sakuyuki1341/wings_steer/各種プログラムテスト/シリアル通信テスト/serial_test_09/read_me.txt

成功したビルド

コマンドラインを実装するための関数群を別ファイルに移行するテスト
