sakuyuki1341/wings_steer/master/steering_master_ver.1.0/analog_stick_ver.1.0.ino

///
/// アナログスティックに関するファイル
///
/****************************************************
 * マクロ部
 ****************************************************/
#include "subs_ver.1.0.h"

/****************************************************
 * 構造体宣言部
 ****************************************************/

/****************************************************
 * 独自関数部
 ****************************************************/
//アナログスティック関連の初期設定
void init_stick() {
	pinMode(PIN_AS_SW, INPUT_PULLUP);
}

//現在のアナログスティックの状態を取得し、返す
analog_stick stick_state() {
	analog_stick tmp;
	tmp.x = analogRead(PIN_AS_X);
	tmp.y = analogRead(PIN_AS_Y);
	tmp.sw = digitalRead(PIN_AS_SW) ? 0 : 1;
	return tmp;
}
