sakuyuki1341/wings_steer/master/steering_master_ver.1.0/memory_ver.1.0.ino

///
/// パラメータの保存に関するファイル
///
/****************************************************
 * マクロ部
 ****************************************************/
#include "subs_ver.1.0.h"

#define MAX_ANGLE_ADDRESS 0	//EEPROMにおけるmax_angleのアドレス
#define STRETCH_ADRESS 1	//EEPROMにおけるstretchのアドレス
#define SPEED_ADRESS 2		//EEPROMにおけるspeedのアドレス
#define C_PS_X_ADRESS 3		//EEPROMにおけるcenterPS_xのアドレス
#define C_PS_Y_ADRESS 4		//EEPROMにおけるcenterPS_yのアドレス

/****************************************************
 * グローバル変数/配列 宣言部
 ****************************************************/
//EEPROMを使う際の初期化。(現在動作なし)
void init_memory() {
	//動作なし
}

// 現在のパラメータを保存する。
void save_parameters() {
	EEPROM.write(MAX_ANGLE_ADDRESS, max_angle);
	EEPROM.write(STRETCH_ADRESS, stretch);
	EEPROM.write(SPEED_ADRESS, speed);
	EEPROM.write(C_PS_X_ADRESS, centerPS_x);
	EEPROM.write(C_PS_Y_ADRESS, centerPS_y);
}

//保存したパラメータを読み込む
void load_parameters() {
	max_angle = EEPROM.read(MAX_ANGLE_ADDRESS);
	stretch = EEPROM.read(STRETCH_ADRESS);
	speed = EEPROM.read(SPEED_ADRESS);
	centerPS_x = EEPROM.read(C_PS_X_ADRESS);
	centerPS_y = EEPROM.read(C_PS_Y_ADRESS);
}
