sakuyuki1341/wings_steer/各種プログラムテスト/シリアル通信テスト/serial_test_11/serial_test_11.ino

/****************************************************
 * マクロ部
 ****************************************************/

/****************************************************
 * 構造体宣言部
 ****************************************************/

/****************************************************
 * プロトタイプ宣言部
 ****************************************************/
void init_cmd();

/****************************************************
 * グローバル変数/配列 宣言部
 ****************************************************/

/****************************************************
 * Arduino 要求関数部
 ****************************************************/
void setup() {
	init_cmd();
}

void loop() {

}

/****************************************************
 * 独自関数部
 ****************************************************/
