sakuyuki1341/wings_steer/各種プログラムテスト/アナログスティック読み込み/analog_test_01/analog_test_01.ino

/****************************************************
 * マクロ部
 ****************************************************/
 #define PIN_X 0
 #define PIN_Y 1

/****************************************************
 * 構造体宣言部
 ****************************************************/

/****************************************************
 * プロトタイプ宣言部
 ****************************************************/

/****************************************************
 * グローバル変数/配列 宣言部
 ****************************************************/
int analog_x = 0;   // アナログスティックのx軸
int analog_y = 0;   // アナログスティックのy軸 

/****************************************************
 * Arduino 要求関数部
 ****************************************************/

void setup() {
    Serial.begin(9600);
}

void loop() {
    analog_x = analogRead(PIN_X);
    analog_y = analogRead(PIN_Y);
    
    Serial.print("x vector: ");
    Serial.print(analog_x);
    Serial.print("  //  y vector: ");
    Serial.println(analog_y);
    Serial.println("===============================================");

    delay(100);  // 毎秒100回処理
}

/****************************************************
 * 独自関数部
 ****************************************************/
