sakuyuki1341/wings_steer/各種プログラムテスト/シリアル通信テスト/serial_test_09/serial_test_09.ino

//コマンドラインを実装するための関数群を別ファイルに移行するテスト
/****************************************************
 * マクロ部
 ****************************************************/
#include <string.h>
#include <MsTimer2.h>

/****************************************************
 * 構造体宣言部
 ****************************************************/

/****************************************************
 * プロトタイプ宣言部
 ****************************************************/
void cmdline();


/****************************************************
 * グローバル変数/配列 宣言部
 ****************************************************/
int loop_num = 0;


/****************************************************
 * Arduino 要求関数部
 ****************************************************/
void setup() {
    Serial.begin(115200, SERIAL_8E1); 
    // コマンドラインのタイマー割り込みセット
    MsTimer2::set(10, cmdline);
    MsTimer2::start();
}

void loop() {
    Serial.println(loop_num++);
    Serial.println("serial_avairable");
    delay(1000);
}

/****************************************************
 * 独自関数部
 ****************************************************/
